lukesturgeon/SyntheticAerialRobotics/Arduino/AccelStepper_x4/Calibrated_AccelStepper.h

class Calibrated_AccelStepper : public AccelStepper
{
  public :

    const float STEPS_PER_MM = 400.0f / 201.0f; // (400steps / 215mm

    Calibrated_AccelStepper(int stepPin, int dirPin, int sensorPin) :
      AccelStepper(AccelStepper::DRIVER, stepPin, dirPin) {
      _stepPin = stepPin;
      _dirPin = dirPin;
      _sensorPin = sensorPin;
      _isCalibrated = _isCalibratingIn = _isCalibratingOut = false;
      _isFreeStepping = false;

      _minSteps = 0;
      _maxSteps = 999999;
    }

    /**
     * Check if the pushbutton is triggered
     */
    bool isSensorBlocked() {
      if (digitalRead(_sensorPin) == HIGH) {
        return true;
      } else {
        return false;
      }
    }

    /**
     * Start the calibration process
     * Next loop() will call runCalibration automatically
     */
    void initCalibration() {
      _isCalibrated = false;
      _isCalibratingIn = true;
      _isCalibratingOut = false;
    }

    void runCalibration()
    {
      if (_isCalibratingIn)
      {
        // pull in cable
        if (isSensorBlocked())
        {
          // we are close enough, start dropping
          moveTo( currentPosition() + 10 );
          _isCalibratingIn = false;
          _isCalibratingOut = true;
        } else {
          // move a little bit closer
          moveTo( currentPosition() - 1 );
        }
      }

      else if (_isCalibratingOut)
      {
        // release more cable
        if (distanceToGo() == 0 && isSensorBlocked())
        {
          // keep droping
          moveTo( currentPosition() + 10 );
        }
        else if (distanceToGo() == 0 && !isSensorBlocked())
        {
          // stop now and calibrate
          _isCalibratingIn = false;
          _isCalibratingOut = false;
          _isCalibrated = true;
          setSpeed(0.0);
          setCurrentPosition(0.0);
          moveTo( 0.0 );
        }
      }

      // call the run function ourselves
      run();
    }

    bool isCalibrating() {
      if (_isCalibratingIn || _isCalibratingOut) {
        return true;
      } else {
        return false;
      }
    }

    bool isCalibrated() {
      return _isCalibrated;
    }

    bool isFreeStepping() {
      return _isFreeStepping;
    }

    void freeStep(int steps) {
      _isFreeStepping = true;

      if (currentPosition() + steps < _minSteps) {
        // go the minimum remaining
        move( _minSteps - currentPosition() );
      } else if (currentPosition() + steps > _maxSteps) {
        // go the max remaining
        move( _maxSteps - currentPosition() );
      } else {
        // just move because it's a safe number
        move( steps );
      }
    }

    void runFreeStep() {
      if (distanceToGo() == 0) {
        _isFreeStepping = false;
      } else {
        run();
      }
    }

    void stepCW() {
      digitalWrite(_dirPin, HIGH);
      digitalWrite(_stepPin, HIGH);
      digitalWrite(_stepPin, LOW);
    }

    void stepCCW() {
      digitalWrite(_dirPin, LOW);
      digitalWrite(_stepPin, HIGH);
      digitalWrite(_stepPin, LOW);
    }

    void moveToMM(float len) {
      long numSteps = long( STEPS_PER_MM * len );

      Serial.print("len:");
      Serial.print(len);
      Serial.print(" = steps:");
      Serial.println(numSteps);

      // constrain
      moveTo( constrain(numSteps, _minSteps, _maxSteps) );
    }

    long currentLengthMM() {
      return currentPosition();
    }

    /**
     * Set the minimum position in steps that motor can move to
     */
    void setMinSteps(int p) {
      _minSteps = p;
    }

    /**
     * Set the maximum position in steps that motor can move to
     */
    void setMaxSteps(int p) {
      _maxSteps = p;
    }

  private:
    bool  _isCalibrated;
    bool  _isCalibratingIn;
    bool  _isCalibratingOut;
    bool  _isFreeStepping;
    int   _stepPin;
    int   _dirPin;
    int   _sensorPin;
    long   _minSteps;
    long   _maxSteps;
};
